Retro-Do-MSX/MsxUsbMouseConverter/Pictures/IMG_3110.JPG

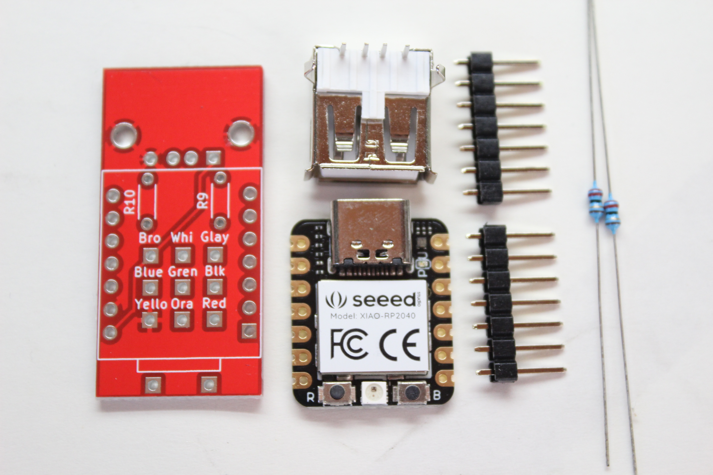
Pictures/IMG_3110.JPG
