Retro-Do-MSX/MsxUsbMouseConverter/Pictures/IMG_3117.JPG

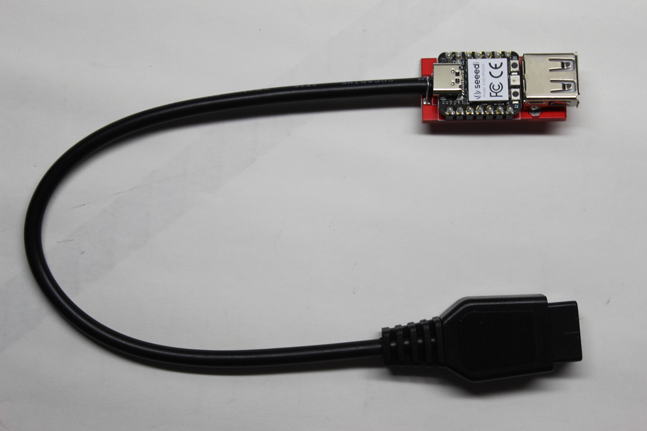
Pictures/IMG_3117.JPG
