Retro-Do-MSX/MsxUsbMouseConverter/Pictures/IMG_3118.JPG

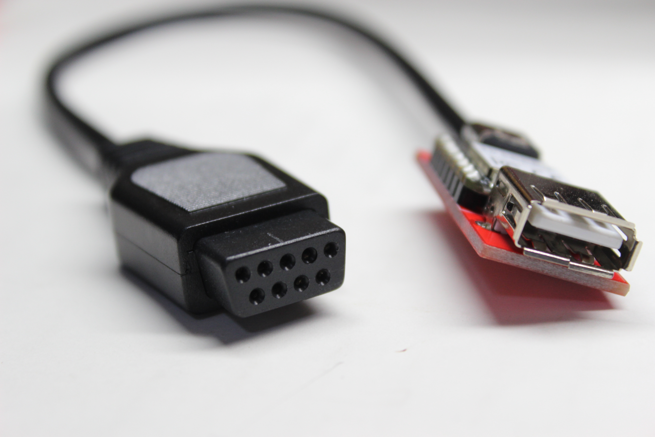
Pictures/IMG_3118.JPG
