Retro-Do-MSX/MsxUsbMouseConverter/Pictures/IMG_3202.JPG

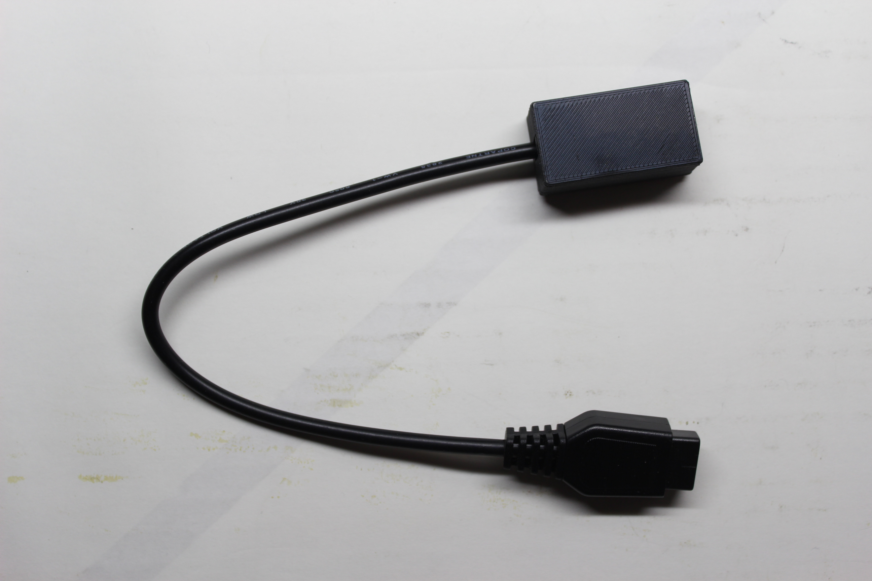
Pictures/IMG_3202.JPG
